naorlivne/arduino_tnt_bomb_defuse_game/hardware/P11002-162008.jpg

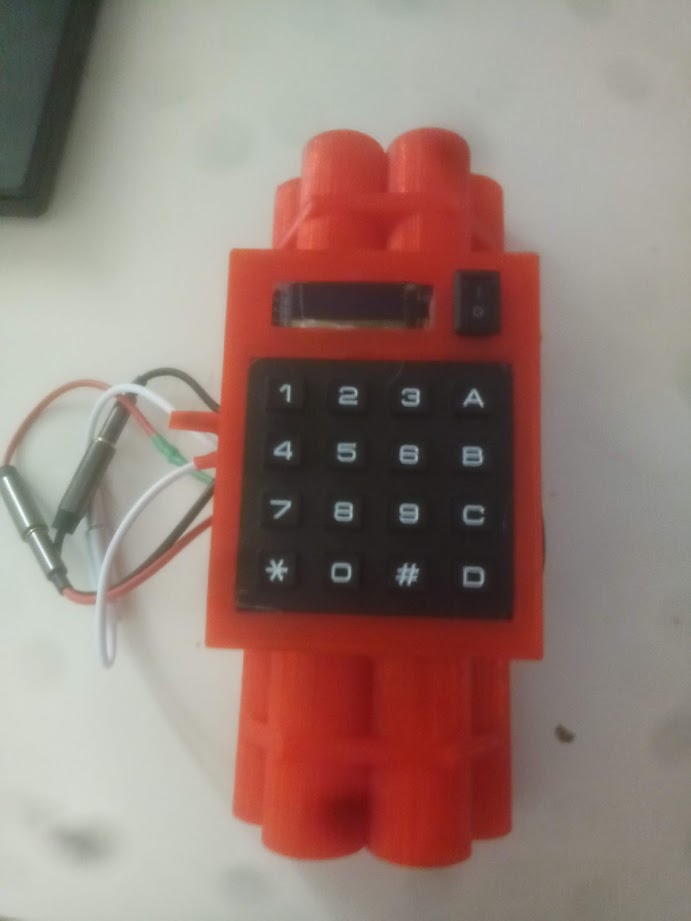
hardware/P11002-162008.jpg
