naorlivne/arduino_tnt_bomb_defuse_game/hardware/P11002-162149.jpg

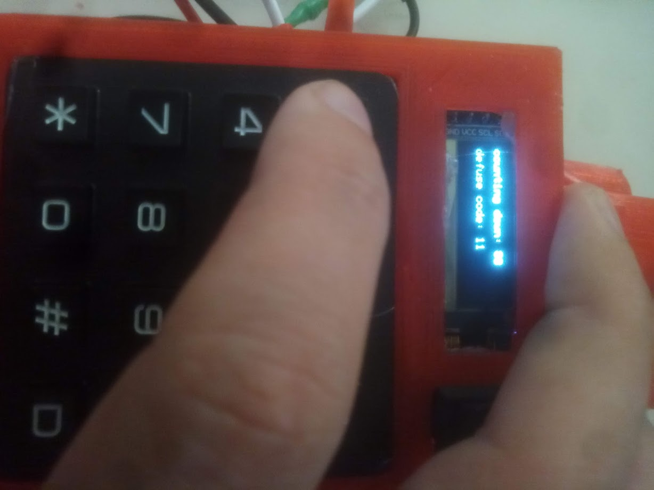
hardware/P11002-162149.jpg
